HolTyc/Pocket-Lab-Power-Supply-STM32/firmware/STM32Firmware/Pocket-Lab-Power-Supply-STM32/Core/Inc/app.h

/* Pocket Lab-Bench Power Supply application logic.
 * Called from main.c: App_Init() once after peripheral init,
 * App_Loop() forever from the main while(1).
 */

#ifndef APP_H
#define APP_H

void App_Init(void);
void App_Loop(void);

#endif /* APP_H */
